bakoontz2/VNA/board-smt/VNA2.kicad_sch

## KiCad design board-smt/VNA2.kicad_sch (2022-07-23)

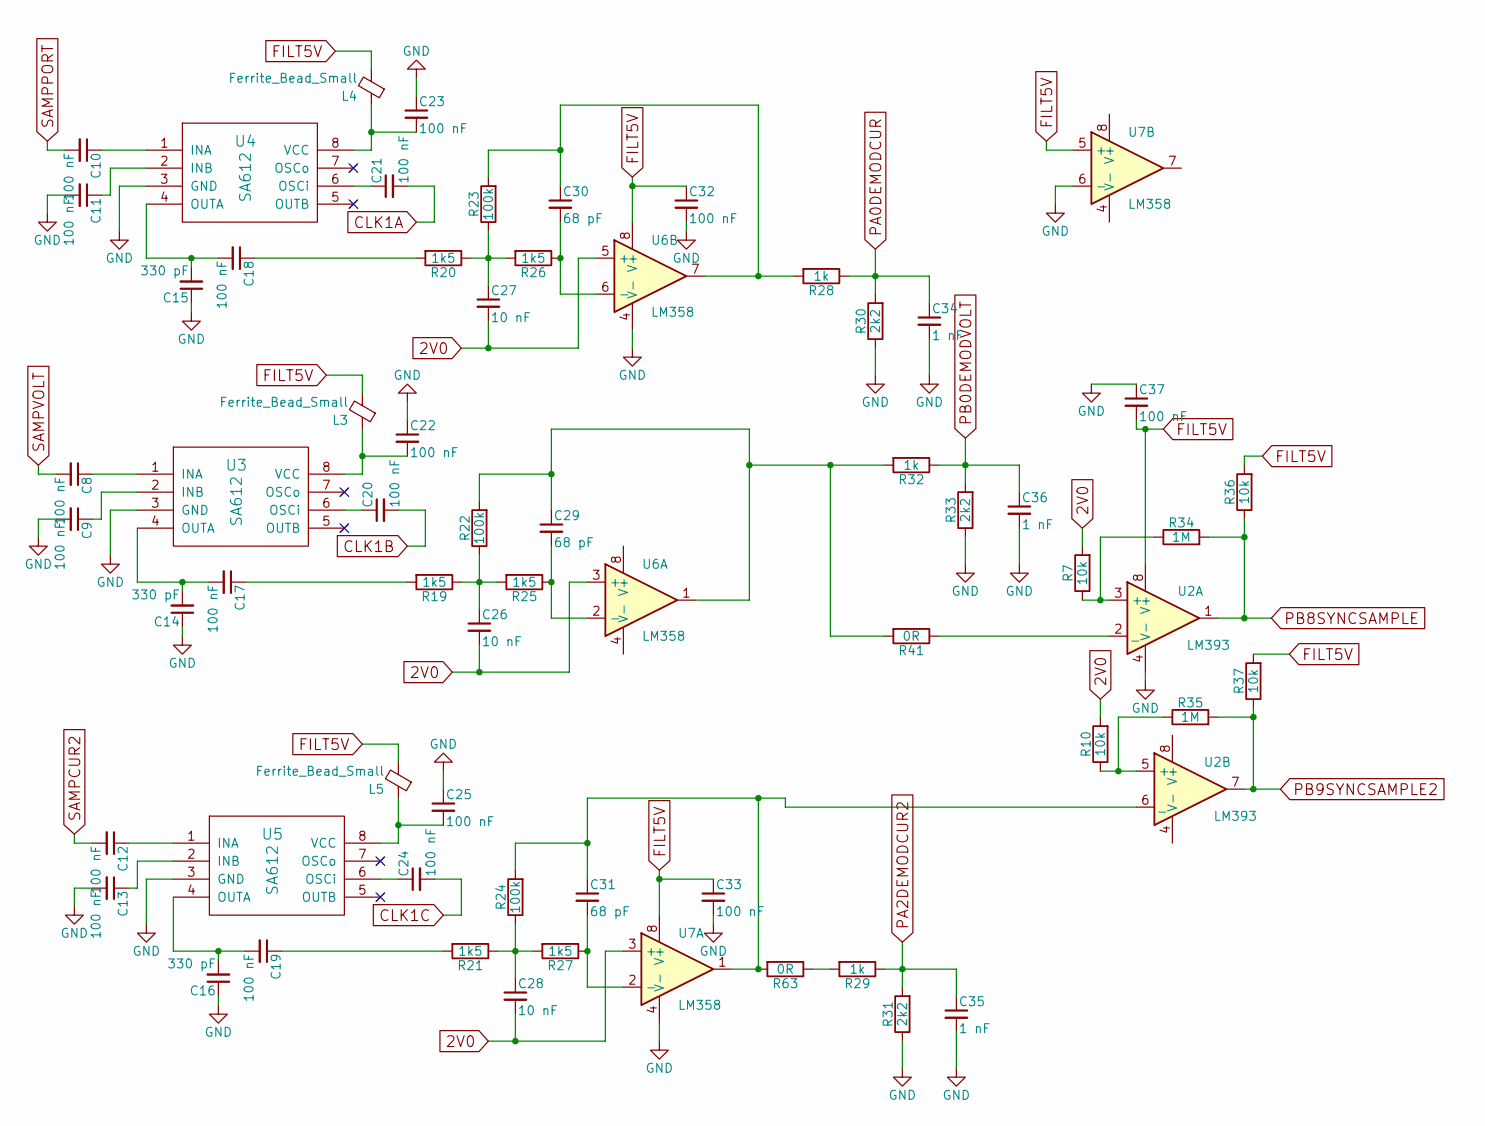
[picture p3: schematic VNA2.kicad_sch]

Parts:
C8, C9, C10, C11, C12, C13, C17, C18, C19, C20, C21, C22, C23, C24, C32, C33: 100 nF; C_0805_HandSoldering; LCSC C49678
C14, C15, C16: 330 pF; C_0805_HandSoldering; LCSC C51207
C25, C37: 100 nF; C_0805_HandSoldering
C26, C27, C28: 10 nF; C_0805_HandSoldering; LCSC C1710
C29, C30, C31: 68 pF; C_0805_HandSoldering; LCSC C1834
C34, C35, C36: 1 nF; C_0805_HandSoldering; LCSC C46653
L3, L4, L5: Ferrite_Bead_Small; L_0805_HandSoldering; LCSC C1015
R7, R10, R36, R37: 10k; R_0805_HandSoldering; LCSC C17414
R19, R20, R21, R25, R26, R27: 1k5; R_0805_HandSoldering; LCSC C4310
R22, R23, R24: 100k; R_0805_HandSoldering; LCSC C17407
R28, R29, R32: 1k; R_0805_HandSoldering; LCSC C17513
R30, R31, R33: 2k2; R_0805_HandSoldering; LCSC C17520
R34, R35: 1M; R_0805_HandSoldering; LCSC C17514
R41, R63: 0R; R_0805_HandSoldering; LCSC C17477
U2: LM393; SOIC-8_3.9x4.9mm_Pitch1.27mm; LCSC C7955
U3, U4, U5: SA612; SOIC-8_3.9x4.9mm_Pitch1.27mm
U6, U7: LM358; SOIC-8_3.9x4.9mm_Pitch1.27mm; LCSC C7950

Connections:
2V0: C26.2, C27.2, C28.2, R7.2, R10.2, U6.3 (+), U6.5 (+), U7.3 (+)
CLK1A: C21.2
CLK1B: C20.2
CLK1C: C24.2
FILT5V: C32.1, C33.1, C37.2, L3.2, L4.2, L5.2, R36.2, R37.2, U2.8 (V+), U6.8 (V+), U7.5 (+), U7.8 (V+)
GND: C9.2, C11.2, C13.2, C14.1, C15.1, C16.1, C22.1, C23.1, C25.1, C32.2, C33.2, C34.2, C35.2, C36.2, C37.1, R30.1, R31.1, R33.1, U2.4 (V-), U3.3 (GND), U4.3 (GND), U5.3 (GND), U6.4 (V-), U7.4 (V-), U7.6 (-)
unnamed: C8.1, U3.1 (INA)
unnamed: C9.1, U3.2 (INB)
unnamed: C10.1, U4.1 (INA)
unnamed: C11.1, U4.2 (INB)
unnamed: C12.1, U5.1 (INA)
unnamed: C13.1, U5.2 (INB)
unnamed: C14.2, C17.2, U3.4 (OUTA)
unnamed: C15.2, C18.2, U4.4 (OUTA)
unnamed: C16.2, C19.2, U5.4 (OUTA)
unnamed: C17.1, R19.2
unnamed: C18.1, R20.2
unnamed: C19.1, R21.2
unnamed: C20.1, U3.6 (OSCi)
unnamed: C21.1, U4.6 (OSCi)
unnamed: C22.2, L3.1, U3.8 (VCC)
unnamed: C23.2, L4.1, U4.8 (VCC)
unnamed: C24.1, U5.6 (OSCi)
unnamed: C25.2, L5.1, U5.8 (VCC)
unnamed: C26.1, R19.1, R22.1, R25.2
unnamed: C27.1, R20.1, R23.1, R26.2
unnamed: C28.1, R21.1, R24.1, R27.2
unnamed: C29.1, R22.2, R32.2, R41.2, U6.1
unnamed: C29.2, R25.1, U6.2 (-)
unnamed: C30.1, R23.2, R28.2, U6.7
unnamed: C30.2, R26.1, U6.6 (-)
unnamed: C31.1, R24.2, R63.2, U2.6 (_), U7.1
unnamed: C31.2, R27.1, U7.2 (-)
unnamed: R10.1, R35.1, U2.5 (+)
unnamed: R29.2, R63.1
unnamed: R7.1, R34.1, U2.3 (+)
unnamed: R41.1, U2.2 (_)
PA0DEMODCUR: C34.1, R28.1, R30.2
PA2DEMODCUR2: C35.1, R29.1, R31.2
PB0DEMODVOLT: C36.1, R32.1, R33.2
PB8SYNCSAMPLE: R34.2, R36.1, U2.1
PB9SYNCSAMPLE2: R35.2, R37.1, U2.7
SAMPCUR2: C12.2
SAMPPORT: C10.2
SAMPVOLT: C8.2
