bakoontz2/VNA/board-smt/VNA.kicad_sch

## KiCad design board-smt/VNA.kicad_sch (2022-07-23)

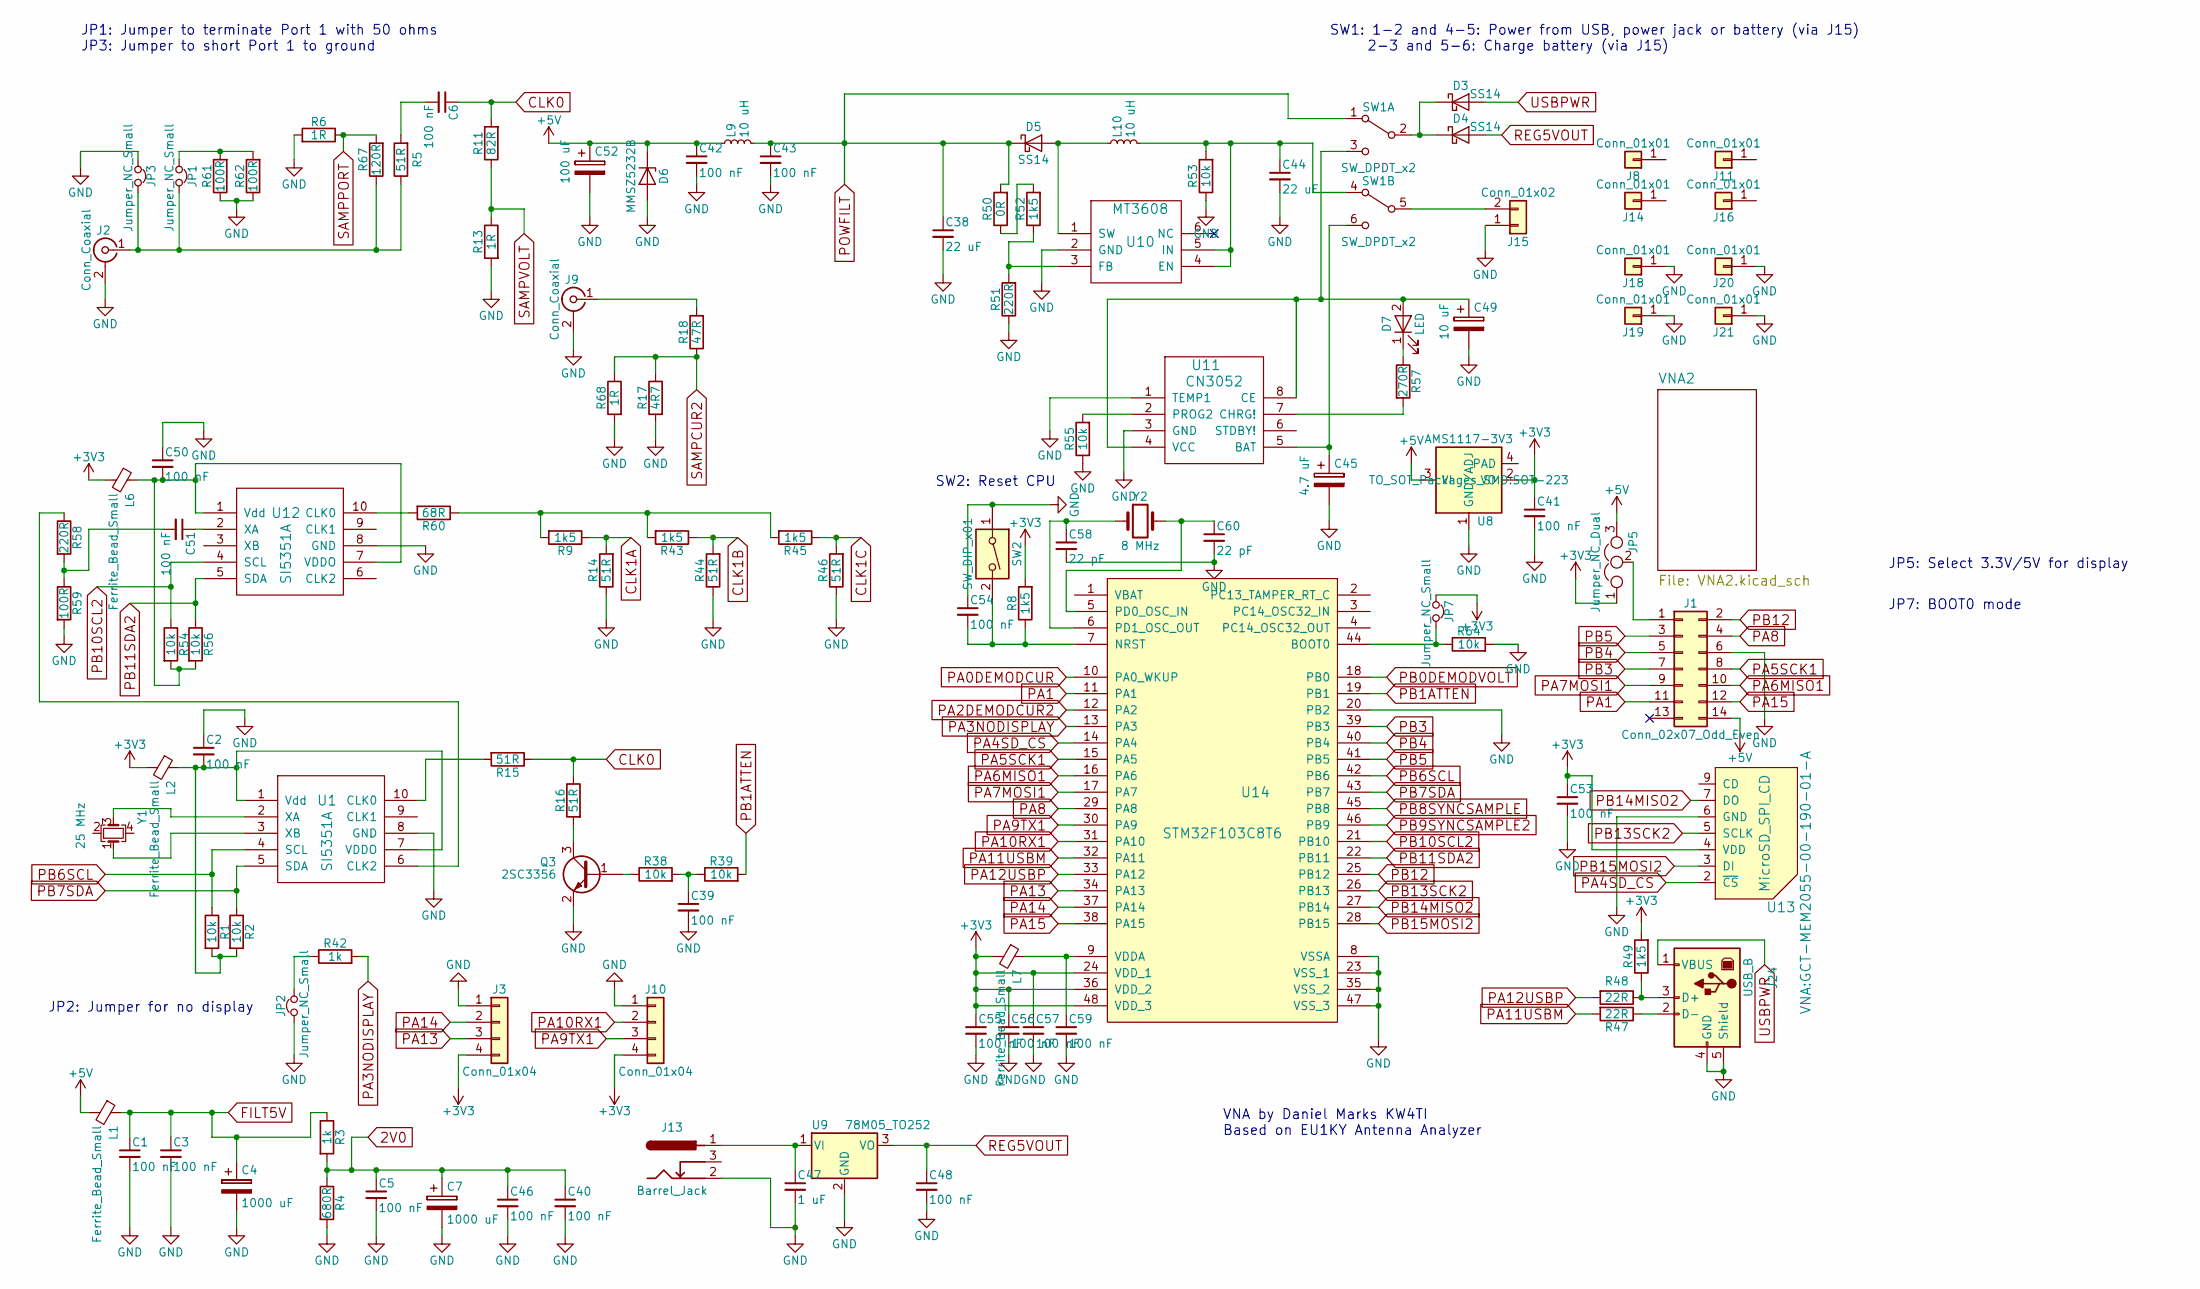
[picture p4: schematic VNA.kicad_sch]

Parts:
C1, C2, C3, C5, C6, C39, C40, C41, C42, C43, C46, C48, C50, C54, C55, C56, C57, C59: 100 nF; C_0805_HandSoldering; LCSC C49678
C4, C7: 1000 uF; CP_Elec_8x10.5
C38, C44: 22 uF; C_1210_HandSoldering
C45: 4.7 uF; CP_Elec_4x4.5
C47: 1 uF; C_0805_HandSoldering; LCSC C28323
C49: 10 uF; CP_Elec_4x4.5
C51, C53: 100 nF; C_0805_HandSoldering
C52: 100 uF; CP_Elec_4x4.5
C58, C60: 22 pF; C_0805_HandSoldering; LCSC C1804
D3, D4, D5: SS14; D_SMA; LCSC C2480
D6: MMSZ5232B; D_MiniMELF; LCSC C8062
D7: LED; LED_0805; LCSC C84256
J1: Conn_02x07_Odd_Even; Pin_Header_Straight_2x07_Pitch2.54mm
J2, J9: Conn_Coaxial; Amphenol_RF_SMA_132289
J3, J10: Conn_01x04; Pin_Header_Straight_1x04_Pitch2.54mm
J8, J11, J14, J16, J18, J19, J20, J21: Conn_01x01; 1pin
J13: Barrel_Jack; BARREL_JACK
J15: Conn_01x02; Molex_KK-6410-02_02x2.54mm_Straight
J24: USB_B
JP1, JP2, JP3, JP7: Jumper_NC_Small; Pin_Header_Straight_1x02_Pitch2.54mm
JP5: Jumper_NC_Dual; Pin_Header_Straight_1x03_Pitch2.54mm
L1, L2, L6, L7: Ferrite_Bead_Small; L_0805_HandSoldering; LCSC C1015
L9, L10: 10 uH; L_7.3x7.3_H4.5
Q3: 2SC3356; SOT-23; LCSC C9659
R1, R2, R38, R39, R53, R54, R55, R56, R64: 10k; R_0805_HandSoldering; LCSC C17414
R3, R42: 1k; R_0805_HandSoldering; LCSC C17513
R4: 680R; R_0805_HandSoldering; LCSC C17798
R5, R14, R15, R16, R44, R46: 51R; R_0805_HandSoldering; LCSC C17738
R6, R13, R68: 1R; R_0805_HandSoldering; LCSC C25271
R8, R9, R43, R45, R49, R52: 1k5; R_0805_HandSoldering; LCSC C4310
R11: 82R; R_0805_HandSoldering; LCSC C17841
R17: 4R7; R_0805_HandSoldering; LCSC C17675
R18: 47R; R_0805_HandSoldering; LCSC C17714
R47, R48: 22R; R_0805_HandSoldering; LCSC C17561
R50: 0R; R_0805_HandSoldering; LCSC C17477
R51, R58: 220R; R_0805_HandSoldering; LCSC C17557
R57: 270R; R_0805_HandSoldering; LCSC C17590
R59, R61, R62: 100R; R_0805_HandSoldering; LCSC C17408
R60: 68R; R_0805_HandSoldering; LCSC C17802
R67: 120R; R_0805_HandSoldering; LCSC C17437
SW1: SW_DPDT_x2; Molex_KK-6410-06_06x2.54mm_Straight
SW2: SW_DIP_x01; SW_PUSH_6mm
U1, U12: SI5351A; MSOP-10_3x3mm_Pitch0.5mm
U8: AMS1117-3V3; SOT-223; MPN LM1117; LCSC C6186
U9: 78M05_TO252; TO-252-3_TabPin2; LCSC C58069
U10: MT3608; SOT-23-6
U11: CN3052; TI_SO-PowerPAD-8
U13: MicroSD_SPI_CD; GCT-MEM2055-00-190-01-A
U14: STM32F103C8T6; LQFP-48_7x7mm_Pitch0.5mm; LCSC C8304
Y1: 25 MHz; Crystal_SMD_3225-4pin_3.2x2.5mm_HandSoldering; LCSC C9006
Y2: 8 MHz; Crystal_SMD_5032-2pin_5.0x3.2mm_HandSoldering; LCSC C115962

Connections:
2V0: C5.1, C7.1, C40.1, C46.1, R3.2, R4.1
+3V3: C41.1, C53.1, C55.1, C56.1, C57.1, J3.4, J10.4, JP5.1, JP7.1, L2.2, L6.2, L7.2, R8.2, R49.2, U8.2 (VO), U13.4 (VDD), U14.24 (VDD_1), U14.36 (VDD_2), U14.48 (VDD_3)
+5V: C42.1, C52.1, D6.1 (K), J1.14, JP5.3, L1.2, L9.1, U8.3 (VI)
CLK0: C6.1, R11.2, R15.1, R16.1
CLK1A: R9.1, R14.2
CLK1B: R43.1, R44.2
CLK1C: R45.1, R46.2
FILT5V: C1.1, C3.1, C4.1, L1.1, R3.1
GND: C1.2, C2.1, C3.2, C4.2, C5.2, C7.2, C38.2, C39.2, C40.2, C41.2, C42.2, C43.2, C44.2, C45.2, C46.2, C47.2, C48.2, C49.2, C50.1, C52.2, C53.2, C54.1, C55.2, C56.2, C57.2, C58.2, C59.2, C60.2, D6.2 (A), J1.6, J2.2 (Ext), J3.1, J9.2 (Ext), J10.1, J13.2, J15.1, J18.1, J19.1, J20.1, J21.1, J24.4 (GND), J24.5 (Shield), JP2.1, JP3.1, Q3.2 (E), R4.2, R6.2, R13.2, R14.1, R17.2, R44.1, R46.1, R51.1, R53.1, R55.1, R59.2, R61.1, R62.1, R64.2, R68.2, SW2.1, U1.8 (GND), U8.1 (GND/ADJ), U9.2 (GND), U10.2 (GND), U11.1 (TEMP1), U11.3 (GND), U12.8 (GND), U13.6 (GND), U14.8 (VSSA), U14.20 (PB2), U14.23 (VSS_1), U14.35 (VSS_2), U14.47 (VSS_3)
unnamed: C2.2, L2.1, R1.2, R2.2, U1.1 (Vdd), U1.7 (VDDO)
unnamed: C6.2, R5.2
unnamed: C39.1, R38.2, R39.1
unnamed: C44.1, L10.2, R53.2, SW1.4 (A), U10.4 (EN), U10.5 (IN)
unnamed: C45.1, SW1.6 (C), U11.5 (BAT)
unnamed: C47.1, J13.1, U9.1 (VI)
unnamed: C49.1, D7.2 (A), SW1.3 (C), U11.4 (VCC), U11.8 (CE)
unnamed: C50.2, L6.1, R54.2, R56.2, U12.1 (Vdd), U12.7 (VDDO)
unnamed: C51.1, U12.2 (XA)
unnamed: C51.2, R58.2, R59.1
unnamed: C54.2, R8.1, SW2.2, U14.7 (NRST)
unnamed: C58.1, U14.6 (PD1_OSC_OUT), Y2.1
unnamed: C59.1, L7.1, U14.9 (VDDA)
unnamed: C60.1, U14.5 (PD0_OSC_IN), Y2.2
unnamed: D3.1 (K), D4.1 (K), SW1.2 (B)
unnamed: D5.2 (A), L10.1, U10.1 (SW)
unnamed: D7.1 (K), R57.1
unnamed: J1.1, JP5.2
unnamed: J2.1 (In), JP1.2, JP3.2, R5.1, R67.1
unnamed: J9.1 (In), R18.2
unnamed: J15.2, SW1.5 (B)
unnamed: J24.2 (D-), R47.1
unnamed: J24.3 (D+), R48.1, R49.1
unnamed: JP1.1, R61.2, R62.2
unnamed: JP2.2, R42.1
unnamed: JP7.2, R64.1, U14.44 (BOOT0)
unnamed: Q3.1 (B), R38.1
unnamed: Q3.3 (C), R16.2
unnamed: R15.2, U1.10 (CLK0)
unnamed: R9.2, R43.2, R45.2, R60.1
unnamed: R50.1, R52.2
unnamed: R51.2, R52.1, U10.3 (FB)
unnamed: R55.2, U11.2 (PROG2)
unnamed: R57.2, U11.7 (CHRG!)
unnamed: R58.1, U1.6 (CLK2)
unnamed: R60.2, U12.10 (CLK0)
unnamed: U1.2 (XA), Y1.3
unnamed: U1.3 (XB), Y1.1
PA0DEMODCUR: U14.10 (PA0_WKUP)
PA1: J1.11, U14.11 (PA1)
PA2DEMODCUR2: U14.12 (PA2)
PA3NODISPLAY: R42.2, U14.13 (PA3)
PA4SD_CS: U13.2 (~CS), U14.14 (PA4)
PA5SCK1: J1.8, U14.15 (PA5)
PA6MISO1: J1.10, U14.16 (PA6)
PA7MOSI1: J1.9, U14.17 (PA7)
PA8: J1.4, U14.29 (PA8)
PA9TX1: J10.3, U14.30 (PA9)
PA10RX1: J10.2, U14.31 (PA10)
PA11USBM: R47.2, U14.32 (PA11)
PA12USBP: R48.2, U14.33 (PA12)
PA13: J3.3, U14.34 (PA13)
PA14: J3.2, U14.37 (PA14)
PA15: J1.12, U14.38 (PA15)
PB0DEMODVOLT: U14.18 (PB0)
PB1ATTEN: R39.2, U14.19 (PB1)
PB3: J1.7, U14.39 (PB3)
PB4: J1.5, U14.40 (PB4)
PB5: J1.3, U14.41 (PB5)
PB6SCL: R1.1, U1.4 (SCL), U14.42 (PB6)
PB7SDA: R2.1, U1.5 (SDA), U14.43 (PB7)
PB8SYNCSAMPLE: U14.45 (PB8)
PB9SYNCSAMPLE2: U14.46 (PB9)
PB10SCL2: R54.1, U12.4 (SCL), U14.21 (PB10)
PB11SDA2: R56.1, U12.5 (SDA), U14.22 (PB11)
PB12: J1.2, U14.25 (PB12)
PB13SCK2: U13.5 (SCLK), U14.26 (PB13)
PB14MISO2: U13.7 (DO), U14.27 (PB14)
PB15MOSI2: U13.3 (DI), U14.28 (PB15)
POWFILT: C38.1, C43.1, D5.1 (K), L9.2, R50.2, SW1.1 (A)
REG5VOUT: C48.1, D4.2 (A), U9.3 (VO)
SAMPCUR2: R17.1, R18.1, R68.1
SAMPPORT: R6.1, R67.2
SAMPVOLT: R11.1, R13.1
USBPWR: D3.2 (A), J24.1 (VBUS)

Notes on the sheet:
SW2: Reset CPU
JP1: Jumper to terminate Port 1 with 50 ohms JP3: Jumper to short Port 1 to ground
JP7: BOOT0 mode
SW1: 1-2 and 4-5: Power from USB, power jack or battery (via J15) 2-3 and 5-6: Charge battery (via J15)
VNA by Daniel Marks KW4TI Based on EU1KY Antenna Analyzer
JP5: Select 3.3V/5V for display
JP2: Jumper for no display
